Ultra-Arcade/open-ua-pcb/Circle WASD Passthrough/CNC Files/CombinedLayers_3mm.dxf

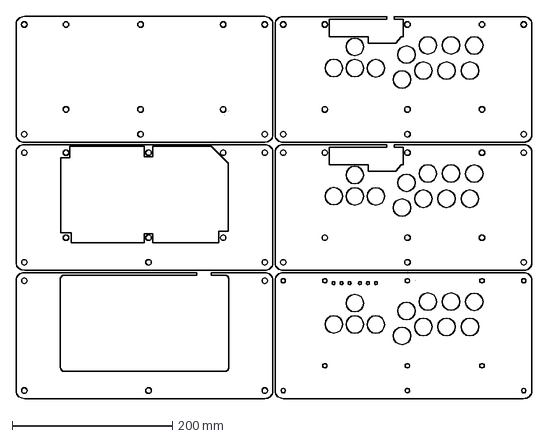
[picture p21: CAD file, 2024-10-16]
Circle WASD Passthrough/CNC Files/CombinedLayers_3mm.dxf
643.0 x 476.7 mm
