Ultra-Arcade/open-ua-pcb/16B Passthrough/CNC Files/Layer3_3mm.dxf

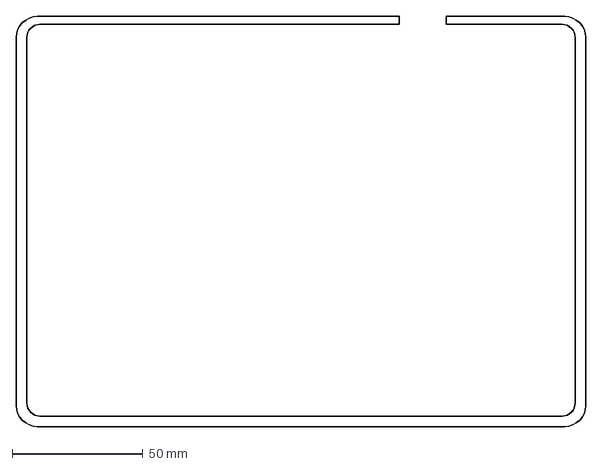
[picture p22: CAD file, 2024-10-16]
16B Passthrough/CNC Files/Layer3_3mm.dxf
218.0 x 157.0 mm
