Ultra-Arcade/open-ua-pcb/Circle WASD Passthrough/CNC Files/Layer1_3mm.dxf

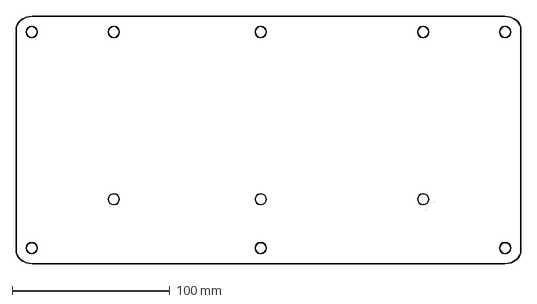
[picture p23: CAD file, 2024-10-16]
Circle WASD Passthrough/CNC Files/Layer1_3mm.dxf
320.0 x 156.9 mm
